mjhaahr/RGB-LED-Pendant/code/Small_Pendant/Util.cpp

/**
 * @file        Util.cpp
 * @module      The Utility Module (UTIL)
 *
 * @brief       Contains Utily Methods and Defines for the Small Pendant Project
 *
 * @author      Matthew Haahr (mjhaahr)
 */
#include "Util.hpp"

// Takes a pixel index and returns the angular offset from 0 (in tengths of a degree), unitless radius (in thousandths), and Percentage of White for ColorWheel
// UINT_FAST16_MAX for center value
const static uint_fast16_t angleLut[NUM_LEDS][3u] = {
   	{741, 7280, 0},
  	{819, 7071, 0},
  	{900, 7000, 0},
  	{981, 7071, 0},
  	{1060, 7280, 0},
  	{1237, 7211, 0},
  	{1166, 6708, 0},
  	{1084, 6325, 0},
  	{995, 6083, 2},
  	{900, 6000, 3},
  	{805, 6083, 2},
  	{716, 6325, 0},
  	{634, 6708, 0},
  	{563, 7211, 0},
  	{450, 7071, 0},
  	{513, 6403, 0},
  	{590, 5831, 5},
  	{682, 5385, 7},
  	{787, 5099, 9},
  	{900, 5000, 9},
  	{1013, 5099, 9},
  	{1118, 5385, 7},
  	{1210, 5831, 5},
  	{1287, 6403, 0},
  	{1350, 7071, 0},
  	{1463, 7211, 0},
  	{1413, 6403, 0},
  	{1350, 5657, 6},
  	{1269, 5000, 9},
  	{1166, 4472, 13},
  	{1040, 4123, 16},
  	{900, 4000, 20},
  	{760, 4123, 16},
  	{634, 4472, 13},
  	{531, 5000, 9},
  	{450, 5657, 6},
  	{387, 6403, 0},
  	{337, 7211, 0},
  	{266, 6708, 0},
  	{310, 5831, 5},
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
      {CENTER, 0, 255},
  	{0, 1000, 160},
  	{0, 2000, 84},
  	{0, 3000, 44},
  	{0, 4000, 20},
  	{0, 5000, 9},
  	{0, 6000, 3},
  	{0, 7000, 0},
  	{3519, 7071, 0},
  	{3505, 6083, 2},
  	{3487, 5099, 9},
  	{3460, 4123, 16},
  	{3416, 3162, 39},
  	{3334, 2236, 71},
  	{3150, 1414, 122},
  	{2700, 1000, 160},
  	{2250, 1414, 122},
  	{2066, 2236, 71},
  	{1984, 3162, 39},
  	{1940, 4123, 16},
  	{1913, 5099, 9},
  	{1895, 6083, 2},
  	{1881, 7071, 0},
  	{1960, 7280, 0},
  	{1984, 6325, 0},
  	{2018, 5385, 7},
  	{2066, 4472, 13},
  	{2137, 3606, 29},
  	{2250, 2828, 49},
  	{2434, 2236, 71},
  	{2700, 2000, 84},
  	{2966, 2236, 71},
  	{3150, 2828, 49},
  	{3263, 3606, 29},
  	{3334, 4472, 13},
  	{3382, 5385, 7},
  	{3416, 6325, 0},
  	{3441, 7280, 0},
  	{3334, 6708, 0},
  	{3290, 5831, 5},
  	{3231, 5000, 9},
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
};

/**
 * Provides a rainbow given a position vlaue
 * The colours are a transition Red -> Green -> Blue -> Red
 * @param uint_fast8_t pos - The 'color wheel position', from 0 to 255
 * @return CRGB - The color data for the given position
 */
CRGB UTIL_Rainbow(uint_fast8_t pos) {
    CRGB outColor;
    if (pos < 85) {
        outColor.red = pos * 3;
        outColor.green = 255 - pos * 3;
        outColor.blue = 0;
    }
    else if (pos < 170) {
        pos -= 85;
        outColor.red = 255 - pos * 3;
        outColor.green = 0;
        outColor.blue = pos * 3;
    }
    else {
        pos -= 170;
        outColor.red = 0;
        outColor.green = pos * 3;
        outColor.blue = 255 - pos * 3;
    }

    return outColor;
}

/**
 * Gets the Polar Coords of the given LED address
 * @param uint_fast8_t led - The LED address
 * @return const uint_fast16_t* [3] - Polar Coordinates of the given LED (angle in tenths of a degree, unitless radius, visual weight percentage from center)
 */
const uint_fast16_t* UTIL_PolarCoords(uint_fast8_t led) {
    return angleLut[led];
}
